dchwebb/QuadMod/QuadMod/src/usb/CDCHandler.cpp

#include "USB.h"
#include "CDCHandler.h"
#include "AudioCodec.h"
#include "EffectManager.h"
#include "Phaser.h"
#include "Flanger.h"
#include "Cordic.h"
#include "Delay.h"
#include <charconv>
#include <stdarg.h>
#include <cmath>

// Check if a command has been received from USB, parse and action as required
void CDCHandler::ProcessCommand()
{
	if (!cmdPending) {
		return;
	}

	const std::string_view cmd {comCmd};

	if (cmd.compare("info") == 0) {		// Print diagnostic information

		sprintf(buf, "Mountjoy QuadMod v1.0 - Current Settings:\r\n\r\n");

		usb->SendString(buf);

	} else if (cmd.compare("help") == 0) {

		usb->SendString("Mountjoy QuadMod\r\n"
				"\r\nSupported commands:\r\n"
				"info           -  Show diagnostic information\r\n"
				"readspi:HH     -  Read codec register at 0xHH\r\n"
				"writespi:RR,VV -  Write value 0xVV to audio codec register 0xRR\r\n"
				//"mreg:AAAAAAAA  -  Get HyperRAM Register at address 0xAAAAAAAA\r\n"
				//"mmem:AAAAAAAA  -  Get HyperRAM Memory at address 0xAAAAAAAA\r\n"
				//"wmem:AAAAAAAA,VVVV  -  Write HyperRAM Memory at address 0xAAAAAAAA\r\n"
				"none           -  No effect\r\n"
				"phaser         -  Set effect to phaser\r\n"
				"delay          -  Delay on/off\r\n"
				"sin:xx.x       -  Sine Test\r\n"
				"filters:x      -  Phaser filter count\r\n"
				"\r\n"
		);

	} else if (cmd.compare("settings") == 0) {
		printf("effect:%s\r\n"
				"delay:%s\r\n"
				"wideflange:%s\r\n"
				"lfoSpeed: %d\r\n"
				"lfoRange: %d\r\n"
				"feedback: %d\r\n"
				"baseFreq: %d\r\n"
				"effectMix: %d\r\n"
				"delayMix: %d\r\n",
				effectManager.effect == &phaser ? "phaser" : "flanger",
				effectManager.delayOn ? "on" : "off",
				flanger.wide ? "on" : "off",
				adc.effectLFOSpeed,
				adc.effectLFORange,
				adc.effectRegen,
				adc.effectLFOBaseFreq,
				adc.effectMix,
				adc.delayMix
				);


	} else if (cmd.compare(0, 8, "filters:") == 0) {
		const int32_t val = ParseInt(cmd, ':', 1, phaser.maxFilters);
		if (val >= 1) {
			phaser.filterCount = val;
		}
		printf("Phaser filter count: %ld\r\n", phaser.filterCount);

	} else if (cmd.compare(0, 9, "lfoSpeed:") == 0) {
		const int32_t val = ParseInt(cmd, ':', 0, 4095);
		if (val >= 0) {
			adc.effectLFOSpeed = val;
		}
		printf("lfoSpeed: %d\r\n", adc.effectLFOSpeed);

	} else if (cmd.compare(0, 9, "lfoRange:") == 0) {
		const int32_t val = ParseInt(cmd, ':', 0, 4095);
		if (val >= 0) {
			adc.effectLFORange = val;
		}
		printf("lfoRange: %d\r\n", adc.effectLFORange);

	} else if (cmd.compare(0, 9, "feedback:") == 0) {
		const int32_t val = ParseInt(cmd, ':', 0, 4095);
		if (val >= 0) {
			adc.effectRegen = val;
		}
		printf("feedback: %d\r\n", adc.effectRegen);

	} else if (cmd.compare(0, 9, "baseFreq:") == 0) {
		const int32_t val = ParseInt(cmd, ':', 0, 4095);
		if (val >= 0) {
			adc.effectLFOBaseFreq = val;
		}
		printf("baseFreq: %d\r\n", adc.effectLFOBaseFreq);

	} else if (cmd.compare(0, 10, "effectMix:") == 0) {
		const int32_t val = ParseInt(cmd, ':', 0, 4095);
		if (val >= 0) {
			adc.effectMix = val;
		}
		printf("effectMix: %d\r\n", adc.effectMix);

	} else if (cmd.compare(0, 9, "delayMix:") == 0) {
		const int32_t val = ParseInt(cmd, ':', 0, 4095);
		if (val >= 0) {
			adc.delayMix = val;
		}
		printf("delayMix: %d\r\n", adc.delayMix);

	} else if (cmd.compare(0, 4, "sin:") == 0) {					// Set envelope duration multiplier
		const float val = ParseFloat(cmd, ':', -10.0f, 10.0f);
		float sin = std::sin(val);
		float cordic = Cordic::Sin(val);
		printf("Sine: %.6f Cordic: %.6f\r\n", sin, cordic);

	} else if (cmd.compare(0, 4, "cos:") == 0) {					// Set envelope duration multiplier
		const float val = ParseFloat(cmd, ':', -10.0f, 10.0f);
		float cos = std::cos(val);
		float cordic = Cordic::Cos(val);
		printf("Cos: %.6f Cordic: %.6f\r\n", cos, cordic);

	} else if (cmd.compare(0, 4, "tan:") == 0) {					// Set envelope duration multiplier
		const float val = ParseFloat(cmd, ':', -10.0f, 10.0f);
		float tan = std::tan(val);
		float cordic = Cordic::Tan(val);
		printf("Tan: %.6f Cordic: %.6f\r\n", tan, cordic);


	} else if (cmd.compare(0, 8, "readspi:") == 0) {				// Read spi register
		uint8_t regNo;
		auto res = std::from_chars(cmd.data() + cmd.find(":") + 1, cmd.data() + cmd.size(), regNo, 16);
		if (res.ec == std::errc()) {
			uint8_t readData = audioCodec.ReadData(regNo);
			printf("SPI Register: %#04x Value: %#04x\r\n", regNo, readData);
		} else {
			usb->SendString("Invalid register\r\n");
		}

	} else if (cmd.compare(0, 9, "writespi:") == 0) {				// write spi register

		uint8_t regNo, value;
		auto res = std::from_chars(cmd.data() + cmd.find(":") + 1, cmd.data() + cmd.size(), regNo, 16);
		if (res.ec == std::errc()) {			// no error
			auto res = std::from_chars(cmd.data() + cmd.find(",") + 1, cmd.data() + cmd.size(), value, 16);
			if (res.ec == std::errc()) {			// no error
				audioCodec.WriteData(regNo, value);
				printf("SPI write: Register: %#04x Value: %#04x\r\n", regNo, value);
			} else {
				usb->SendString("Invalid value\r\n");
			}
		} else {
			usb->SendString("Invalid register\r\n");
		}


	} else if (cmd.compare("none") == 0) {
		effectManager.effect = nullptr;

	} else if (cmd.compare("phaser") == 0) {
		effectManager.effect = &phaser;
		printf("Effect set to phaser\r\n");

	} else if (cmd.compare("flanger") == 0) {
		effectManager.effect = &flanger;
		printf("Effect set to flanger\r\n");

	} else if (cmd.compare("delay") == 0) {
		effectManager.delayOn = !effectManager.delayOn;
		printf("delay:%s\r\n", effectManager.delayOn ? "on" : "off");

	} else if (cmd.compare("wideflange") == 0) {
		flanger.wide = !flanger.wide;
		printf("Wide flanger:%s\r\n", flanger.wide ? "on" : "off");

	} else if (cmd.compare("savecfg") == 0) {			// Save configuration
		//config.SaveConfig();

	} else if (cmd.compare("erasecfg") == 0) {			// Erase config settings
		//config.EraseConfig();

	} else {
		printf("Unrecognised command: %s\r\nType 'help' for supported commands\r\n", cmd.data());
	}

	cmdPending = false;
}


void CDCHandler::PrintString(const char* format, ...)
{
	va_list args;
	va_start (args, format);
	vsnprintf (buf, bufSize, format, args);
	va_end (args);

	usb->SendString(buf);
}


char* CDCHandler::HexToString(const uint8_t* v, uint32_t len, const bool spaces)
{
	const uint8_t byteLen = spaces ? 3 : 2;
	uint32_t pos = 0;
	len = std::min(maxStrLen / byteLen, len);

	for (uint8_t i = 0; i < len; ++i) {
		pos += sprintf(&stringBuf[pos], spaces ? "%02X " : "%02X", v[i]);
	}

	return (char*)&stringBuf;
}


char* CDCHandler::HexToString(const uint16_t v)
{
	sprintf(stringBuf, "%04X", v);
	return (char*)&stringBuf;
}


void CDCHandler::DataIn()
{

}


// As this is called from an interrupt assign the command to a variable so it can be handled in the main loop
void CDCHandler::DataOut()
{
	// Check if sufficient space in command buffer
	const uint32_t newCharCnt = std::min(outBuffCount, maxCmdLen - 1 - buffPos);

	strncpy(&comCmd[buffPos], (char*)outBuff, newCharCnt);
	buffPos += newCharCnt;

	// Check if cr has been sent yet
	if (comCmd[buffPos - 1] == 13 || comCmd[buffPos - 1] == 10 || buffPos == maxCmdLen - 1) {
		comCmd[buffPos - 1] = '\0';
		cmdPending = true;
		buffPos = 0;
	}
}


void CDCHandler::ActivateEP()
{
	EndPointActivate(USBMain::CDC_In,   Direction::in,  EndPointType::Bulk);			// Activate CDC in endpoint
	EndPointActivate(USBMain::CDC_Out,  Direction::out, EndPointType::Bulk);			// Activate CDC out endpoint
	EndPointActivate(USBMain::CDC_Cmd,  Direction::in,  EndPointType::Interrupt);		// Activate Command IN EP

	EndPointTransfer(Direction::out, USBMain::CDC_Out, USBMain::ep_maxPacket);
}


void CDCHandler::ClassSetup(usbRequest& req)
{
	if (req.RequestType == DtoH_Class_Interface && req.Request == GetLineCoding) {
		SetupIn(req.Length, (uint8_t*)&lineCoding);
	}

	if (req.RequestType == HtoD_Class_Interface && req.Request == SetLineCoding) {
		// Prepare to receive line coding data in ClassSetupData
		usb->classPendingData = true;
		EndPointTransfer(Direction::out, 0, req.Length);
	}
}


void CDCHandler::ClassSetupData(usbRequest& req, const uint8_t* data)
{
	// ClassSetup passes instruction to set line coding - this is the data portion where the line coding is transferred
	if (req.RequestType == HtoD_Class_Interface && req.Request == SetLineCoding) {
		lineCoding = *(LineCoding*)data;
	}
}


int32_t CDCHandler::ParseInt(const std::string_view cmd, const char precedingChar, const int32_t low, const int32_t high) {
	int32_t val = -1;
	const int8_t pos = cmd.find(precedingChar);		// locate position of character preceding
	if (pos >= 0 && std::strspn(&cmd[pos + 1], "0123456789-") > 0) {
		val = std::stoi(&cmd[pos + 1]);
	}
	if (high > low && (val > high || val < low)) {
		printf("Must be a value between %ld and %ld\r\n", low, high);
		return low - 1;
	}
	return val;
}


float CDCHandler::ParseFloat(const std::string_view cmd, const char precedingChar, const float low = 0.0f, const float high = 0.0f) {
	float val = -1.0f;
	const int8_t pos = cmd.find(precedingChar);		// locate position of character preceding
	if (pos >= 0 && std::strspn(&cmd[pos + 1], "0123456789.") > 0) {
		val = std::stof(&cmd[pos + 1]);
	}
	if (high > low && (val > high || val < low)) {
		printf("Must be a value between %f and %f\r\n", low, high);
		return low - 1.0f;
	}
	return val;
}


// Descriptor definition here as requires constants from USB class
const uint8_t CDCHandler::Descriptor[] = {
	// IAD Descriptor - Interface association descriptor for CDC class
	0x08,									// bLength (8 bytes)
	USBMain::IadDescriptor,					// bDescriptorType
	USBMain::CDCCmdInterface,				// bFirstInterface
	0x02,									// bInterfaceCount
	0x02,									// bFunctionClass (Communications and CDC Control)
	0x02,									// bFunctionSubClass
	0x01,									// bFunctionProtocol
	USBMain::CommunicationClass,			// String Descriptor

	// Interface Descriptor
	0x09,									// bLength: Interface Descriptor size
	USBMain::InterfaceDescriptor,			// bDescriptorType: Interface
	USBMain::CDCCmdInterface,				// bInterfaceNumber: Number of Interface
	0x00,									// bAlternateSetting: Alternate setting
	0x01,									// bNumEndpoints: 1 endpoint used
	0x02,									// bInterfaceClass: Communication Interface Class
	0x02,									// bInterfaceSubClass: Abstract Control Model
	0x01,									// bInterfaceProtocol: Common AT commands
	USBMain::CommunicationClass,			// iInterface

	// Header Functional Descriptor
	0x05,									// bLength: Endpoint Descriptor size
	USBMain::ClassSpecificInterfaceDescriptor,	// bDescriptorType: CS_INTERFACE
	0x00,									// bDescriptorSubtype: Header Func Desc
	0x10,									// bcdCDC: spec release number
	0x01,

	// Call Management Functional Descriptor
	0x05,									// bFunctionLength
	USBMain::ClassSpecificInterfaceDescriptor,	// bDescriptorType: CS_INTERFACE
	0x01,									// bDescriptorSubtype: Call Management Func Desc
	0x00,									// bmCapabilities: D0+D1
	0x01,									// bDataInterface: 1

	// ACM Functional Descriptor
	0x04,									// bFunctionLength
	USBMain::ClassSpecificInterfaceDescriptor,	// bDescriptorType: CS_INTERFACE
	0x02,									// bDescriptorSubtype: Abstract Control Management desc
	0x02,									// bmCapabilities

	// Union Functional Descriptor
	0x05,									// bFunctionLength
	USBMain::ClassSpecificInterfaceDescriptor,	// bDescriptorType: CS_INTERFACE
	0x06,									// bDescriptorSubtype: Union func desc
	0x00,									// bMasterInterface: Communication class interface
	0x01,									// bSlaveInterface0: Data Class Interface

	// Endpoint 2 Descriptor
	0x07,									// bLength: Endpoint Descriptor size
	USBMain::EndpointDescriptor,			// bDescriptorType: Endpoint
	USBMain::CDC_Cmd,						// bEndpointAddress
	USBMain::Interrupt,						// bmAttributes: Interrupt
	0x08,									// wMaxPacketSize
	0x00,
	0x10,									// bInterval

	//---------------------------------------------------------------------------

	// Data class interface descriptor
	0x09,									// bLength: Endpoint Descriptor size
	USBMain::InterfaceDescriptor,			// bDescriptorType:
	USBMain::CDCDataInterface,				// bInterfaceNumber: Number of Interface
	0x00,									// bAlternateSetting: Alternate setting
	0x02,									// bNumEndpoints: Two endpoints used
	0x0A,									// bInterfaceClass: CDC
	0x00,									// bInterfaceSubClass:
	0x00,									// bInterfaceProtocol:
	0x00,									// iInterface:

	// Endpoint OUT Descriptor
	0x07,									// bLength: Endpoint Descriptor size
	USBMain::EndpointDescriptor,			// bDescriptorType: Endpoint
	USBMain::CDC_Out,						// bEndpointAddress
	USBMain::Bulk,							// bmAttributes: Bulk
	LOBYTE(USBMain::ep_maxPacket),			// wMaxPacketSize:
	HIBYTE(USBMain::ep_maxPacket),
	0x00,									// bInterval: ignore for Bulk transfer

	// Endpoint IN Descriptor
	0x07,									// bLength: Endpoint Descriptor size
	USBMain::EndpointDescriptor,			// bDescriptorType: Endpoint
	USBMain::CDC_In,						// bEndpointAddress
	USBMain::Bulk,							// bmAttributes: Bulk
	LOBYTE(USBMain::ep_maxPacket),			// wMaxPacketSize:
	HIBYTE(USBMain::ep_maxPacket),
	0x00,									// bInterval: ignore for Bulk transfer
};


uint32_t CDCHandler::GetInterfaceDescriptor(const uint8_t** buffer) {
	*buffer = Descriptor;
	return sizeof(Descriptor);
}
