dchwebb/QuadMod/QuadMod/src/Flanger.cpp

#include "Flanger.h"
#include "EffectManager.h"
#include "Cordic.h"
#include <cmath>

// Code loosely based on:
// https://code.soundsoftware.ac.uk/projects/audio_effects_textbook_code/repository/show/effects/flanger/Source

Flanger flanger;


void Flanger::GetSamples(Samples& samples)
{
	const uint32_t lfoFreq = (4095 - adc.effectLFOSpeed) * 128;
	uint32_t lfoPhase = lfoInitPhase + lfoFreq;
	lfoInitPhase = lfoPhase;

	// needs to be between baseFrequency and audioBuffSize
	const float lfoSweepWidthADC = (adc.effectLFORange / 4096.0f) * 100.0f;
	const float regenADC = (4095 - adc.effectRegen) / 4096.0f;
	const float baseFreqADC = ((4095 - adc.effectLFOBaseFreq) / 4096.0f) * 2000.0f;

	// Smooth adc values (particularly to prevent crackling when lfo pos jumps)
	lfoSweepWidth = (lfoSweepWidth * 0.9f) + (0.1f * lfoSweepWidthADC);
	regen = (regen * 0.9f) + (0.1f * regenADC);
	baseFreq = (baseFreq * 0.99f) + (0.01f * baseFreqADC);

	if (++writePos == effectManager.audioBuffSize) {
		writePos = 0;
	}
	Samples wideFlange;

	for (uint32_t channel = 0; channel < 4; ++channel) {

		// Calculate read position
		const float lfoPos = (0.5f + 0.5f * Cordic::Sin(lfoPhase));		// LFO sine wave scaled from 0 to 1
		const float readOffset = 2.0f + baseFreq + (lfoSweepWidth * lfoPos);
		const float flangeSample = SampleFromReadOffset(readOffset, channel);

		// Create a second lfo in anti-phase with the first to get two samples for stereo chorussing effects
		if (wide) {
			const float readOffset2 = 2.0f + baseFreq + (lfoSweepWidth * (1.0f - lfoPos));
			wideFlange.ch[channel] = SampleFromReadOffset(readOffset2, channel);
		}

		effectManager.audioBuffer[writePos].ch[channel] = samples.ch[channel] + regen * flangeSample;

		samples.ch[channel] = flangeSample;

		if (channel > 0) {
			static constexpr uint32_t phaseDiff = std::pow(2, 30);		// Apply a 45 degree phase shift to each channel
			lfoPhase += phaseDiff;
		}
	}

	// Add in some stereo sample
	if (wide) {
		for (uint32_t channel = 0; channel < 4; ++channel) {
			samples.ch[channel] += wideFlange.ch[(channel + 1) & 3] * 0.5f;
		}
	}

	// Convert phase to a 12 bit value for LED brightness
	uint32_t brightness = lfoInitPhase >> 19;		// Limit from 0 to 8191
	if (brightness > 4095) {
		brightness = 8192 - brightness;
	}
	lfoLED = brightness;
}


float Flanger::SampleFromReadOffset(const float readOffset, const uint32_t channel)
{
	float readPos = (float)writePos - readOffset;
	while (readPos <= -1.0f) {
		readPos += effectManager.audioBuffSize;
	}

	// Interpolate two samples
	int32_t floor = std::floor(readPos);

	const float fractionalPos = readPos - (float)floor;				// Handle situation where sample position is between -1 and 0
	if (floor < 0) {
		floor += effectManager.audioBuffSize;
	}

	int32_t ceil = std::ceil(readPos);
	if (ceil >= static_cast<float>(effectManager.audioBuffSize)) {
		ceil -= effectManager.audioBuffSize;
	}

	return std::lerp(effectManager.audioBuffer[floor].ch[channel], effectManager.audioBuffer[ceil].ch[channel], fractionalPos);
}
