dchwebb/QuadMod/QuadMod/src/initialisation.h

#pragma once

#include "stm32h563xx.h"
#include "GpioPin.h"
#include <numbers>

extern volatile uint32_t SysTickVal;
static constexpr uint32_t sysTick = 1000;						// 1ms
static constexpr uint32_t sampleRate = 48000;
static constexpr float inverseSampleRate  = 1.0f / (float)sampleRate;
static constexpr float pi = std::numbers::pi_v<float>;
static constexpr float pi_x_2 = pi * 2.0f;

#ifndef M_PI_4
#define M_PI_4 0.78539816339744830962f
#define M_1_PI 0.63661977236758134308f
#endif

struct ADCValues {
	uint16_t effectMix;
	uint16_t effectLFORange;
	uint16_t effectLFOSpeed;
	uint16_t effectLFOBaseFreq;
	uint16_t effectRegen;
	uint16_t delayTimePot;
	uint16_t delayTimeCV;
	uint16_t delayFeedback;
	uint16_t delayFilter;
	uint16_t delayMix;
};
extern volatile ADCValues adc;


struct DMALinkedList {
	uint32_t TR1;
	uint32_t TR2;
	uint32_t BR1;
	uint32_t SAR;
	uint32_t DAR;
	uint32_t LLR;
};


void InitSystemClock();
void InitSAI();
void InitHardware();
void InitAudioCodec();
void InitSysTick();
void InitMPU();
void InitADC2(volatile uint16_t* buffer, uint16_t channels);
void InitCordic();
void InitPWMTimer();
