dchwebb/QuadMod/QuadMod/src/Flanger.h

#pragma once
#include "initialisation.h"
#include "Effect.h"


class Flanger : public Effect {
public:
	void GetSamples(Samples& samples);
	bool wide = true;
private:
	float SampleFromReadOffset(const float readOffset, const uint32_t channel);

	int32_t writePos = 0;
	uint32_t lfoInitPhase = 0;

	float baseFreq;		// Used for adc smoothing
	float regen;
	float lfoSweepWidth;

	volatile uint32_t& lfoLED = TIM4->CCR2;
};

extern Flanger flanger;
