dchwebb/QuadMod/QuadMod/src/Phaser.h

#pragma once
#include "initialisation.h"
#include "Effect.h"


class Phaser : public Effect {
public:
	void GetSamples(Samples& samples);

	static constexpr uint32_t maxFilters = 16;	// Maximum number of allpass filters to use per channel
	uint32_t filterCount = 4;					// number of allpass filters to use per channel

private:
	float FilterSamples(const uint32_t channel, const float sample, const float lfoSweepWidth, const uint32_t phase);

	struct {
		float coeff;							// Filter co-efficient (simplified)
		float oldVal[maxFilters + 1];			// Previous samples
	} allpass[maxFilters];

	uint32_t lfoInitPhase = 0;
	uint32_t lfoFreq = 0;						// LFO frequency

	volatile uint32_t& lfoLED = TIM4->CCR2;
};

extern Phaser phaser;
